skjdghsdjgsdj/noisy-gif-player/software/Arduino/Application.h

#pragma once
#include <Arduino.h>

class Application {
public:
  Application();

  void setup();
  void loopOnce();

private:
  [[noreturn]] void enterDeepSleep();      // High-level entry point for deep sleep

  void setupPinsAndPower();
  void setupDisplay();
  void setupStorage();
  void setupSubsystems();

  void fadeBacklightOff();
  void powerDownPeripherals();
  [[noreturn]] void startESPDeepSleep();
};
