skjdghsdjgsdj/noisy-gif-player/software/Arduino/GifRenderer.h

#pragma once
#include <Arduino.h>
#include <Adafruit_GFX.h>
#include <Adafruit_ST7789.h>
#include <AnimatedGIF.h>
#include <FS.h>
#include <freertos/FreeRTOS.h>
#include <freertos/queue.h>
#include <freertos/semphr.h>

class GifRenderer {
public:
  static GifRenderer &instance();

  void begin(Adafruit_ST7789 &display);
  bool playGif(const String &gifPath);

  void *openFile(const char *fname, int32_t *pSize);
  void  closeFile(void *pHandle);
  int32_t readFile(GIFFILE *pFile, uint8_t *pBuf, int32_t iLen);
  int32_t seekFile(GIFFILE *pFile, int32_t iPosition);
  void  draw(GIFDRAW *pDraw);

  // Authoritative display size for the project; used by other modules for layout.
  static constexpr int DISPLAY_WIDTH  = 240;
  static constexpr int DISPLAY_HEIGHT = 135;

private:
  GifRenderer();

  static constexpr int FRAMEBUFFER_SIZE = DISPLAY_WIDTH * DISPLAY_HEIGHT;

  Adafruit_ST7789 *tft;
  AnimatedGIF gif;
  File gifFile;
  uint16_t          frameBuffer[2][FRAMEBUFFER_SIZE];
  int               decodeBuffer;
  bool              skipFrame;               // set before gif.playFrame(); read in flushFrameIfLastLine()
  bool              prevFrameWasOpaque;      // true if the last decoded frame had no transparent pixels
  bool              currentFrameHasTransparency; // reset each frame; set by draw() if any scanline is transparent
  // Passed through displayQueue so the DisplayWriter knows which framebuffer
  // rows were actually modified. Sending only the dirty rows reduces SPI
  // transfer time proportionally when the GIF frame covers less than the full
  // canvas height (which is typical with diff_mode=rectangle encoding).
  struct DisplayFrame {
    int bufIdx;
    int topRow;
    int numRows;
  };

  QueueHandle_t     displayQueue;
  SemaphoreHandle_t bufferFree[2];
  TaskHandle_t      displayWriterHandle;

  void clearFrameBuffer();

  bool clipAndPrepareLine(GIFDRAW *pDraw, int &iWidth, int &y, uint8_t *&pixels, uint16_t *&lineBase);
  void applyDisposalIfNeeded(GIFDRAW *pDraw, uint8_t *pixels, int iWidth);
  void drawTransparentLine(GIFDRAW *pDraw, uint8_t *pixels, int iWidth, uint16_t *lineBase, uint16_t *palette);
  void drawOpaqueLine(uint8_t *pixels, int iWidth, uint16_t *lineBase, uint16_t *palette);
  void flushFrameIfLastLine(GIFDRAW *pDraw);

  static void displayWriterTaskEntry(void *param);
  void        displayWriterTask();
  void        startDisplayWriterTask();
  void        stopDisplayWriterTask();
  void        waitForLastFrame(int lastPosted);
};

// Free-function callbacks for AnimatedGIF
void *GIFOpenFile(const char *fname, int32_t *pSize);
void GIFCloseFile(void *pHandle);
int32_t GIFReadFile(GIFFILE *pFile, uint8_t *pBuf, int32_t iLen);
int32_t GIFSeekFile(GIFFILE *pFile, int32_t iPosition);
void GIFDraw(GIFDRAW *pDraw);
